mhorimoto/M304B/InputSwitch.kicad_sch

## KiCad design InputSwitch.kicad_sch (2024-06-09)

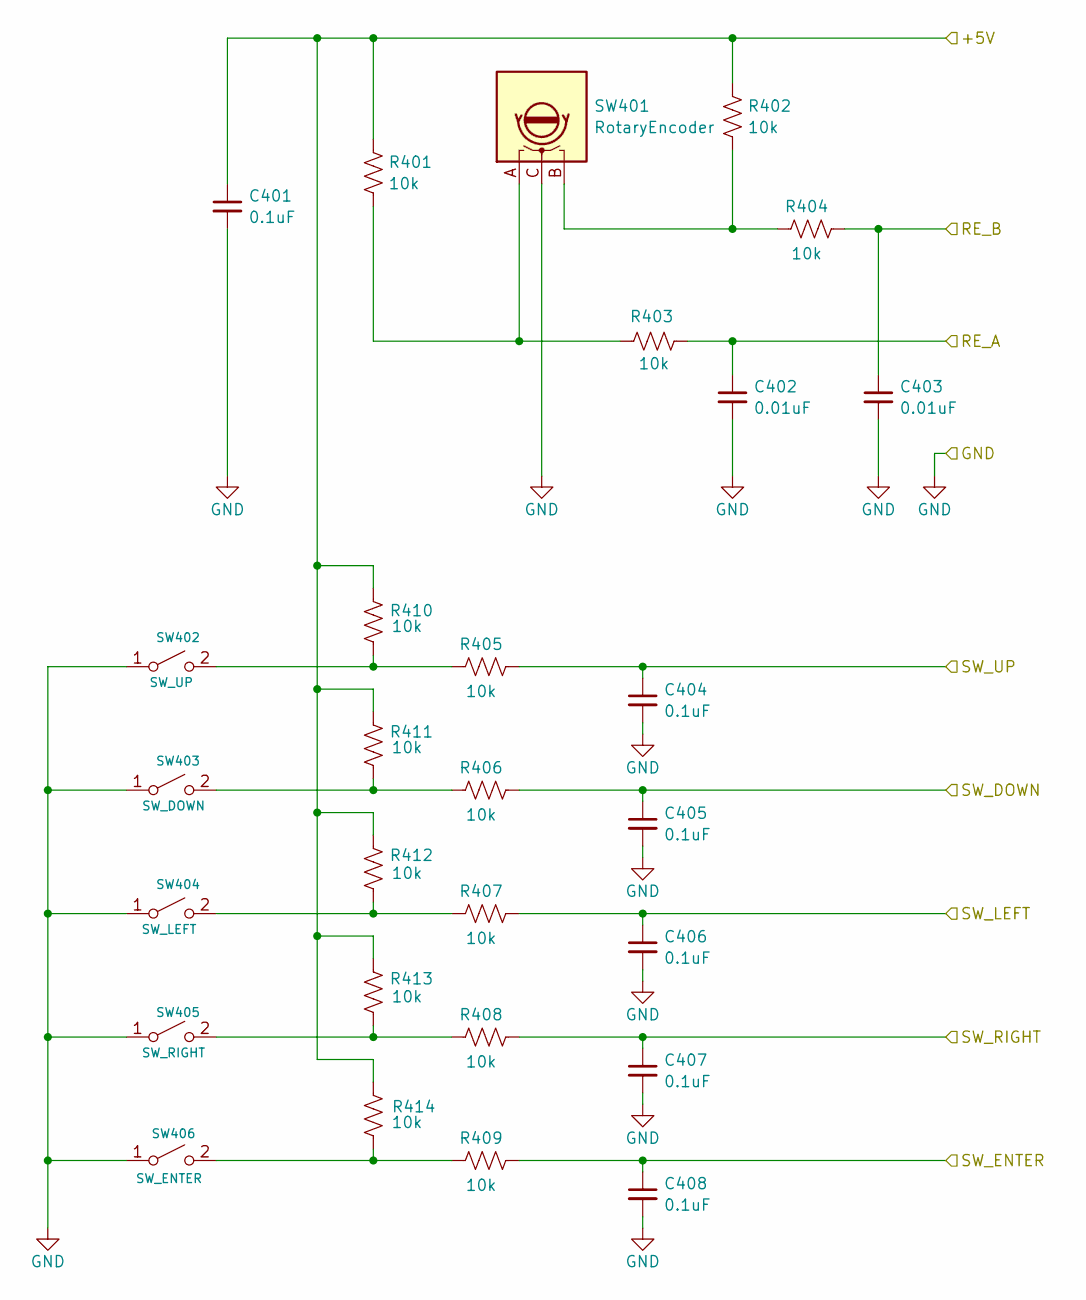
[picture p6: schematic InputSwitch.kicad_sch]

Parts:
C401, C404, C405, C406, C407, C408: 0.1uF; C_Disc_D3.0mm_W2.0mm_P2.50mm
C402, C403: 0.01uF; C_Disc_D3.0mm_W2.0mm_P2.50mm
R401, R402, R403, R404, R405, R406, R407, R408, R409, R410, R411, R412, R413, R414: 10k
SW401: RotaryEncoder; RotaryEncoder_Alps_EC12E_Vertical_H20mm
SW402: SW_UP; TVDT18-050
SW403: SW_DOWN; TVDT18-050
SW404: SW_LEFT; TVDT18-050
SW405: SW_RIGHT; TVDT18-050
SW406: SW_ENTER; TVDT18-050

Connections:
+5V: C401.1, R401.1, R402.1, R410.2, R411.2, R412.2, R413.2, R414.2
GND: C401.2, C402.2, C403.2, C404.2, C405.2, C406.2, C407.2, C408.2, SW401.C, SW402.1 (A), SW403.1 (A), SW404.1 (A), SW405.1 (A), SW406.1 (A)
unnamed: R401.2, R403.1, SW401.A
unnamed: R402.2, R404.1, SW401.B
unnamed: R405.1, R410.1, SW402.2 (B)
unnamed: R406.1, R411.1, SW403.2 (B)
unnamed: R407.1, R412.1, SW404.2 (B)
unnamed: R408.1, R413.1, SW405.2 (B)
unnamed: R409.1, R414.1, SW406.2 (B)
RE_A: C402.1, R403.2
RE_B: C403.1, R404.2
SW_DOWN: C405.1, R406.2
SW_ENTER: C408.1, R409.2
SW_LEFT: C406.1, R407.2
SW_RIGHT: C407.1, R408.2
SW_UP: C404.1, R405.2
