mhorimoto/M304B/M304B.kicad_sch

## KiCad design M304B.kicad_sch (2024-06-09)

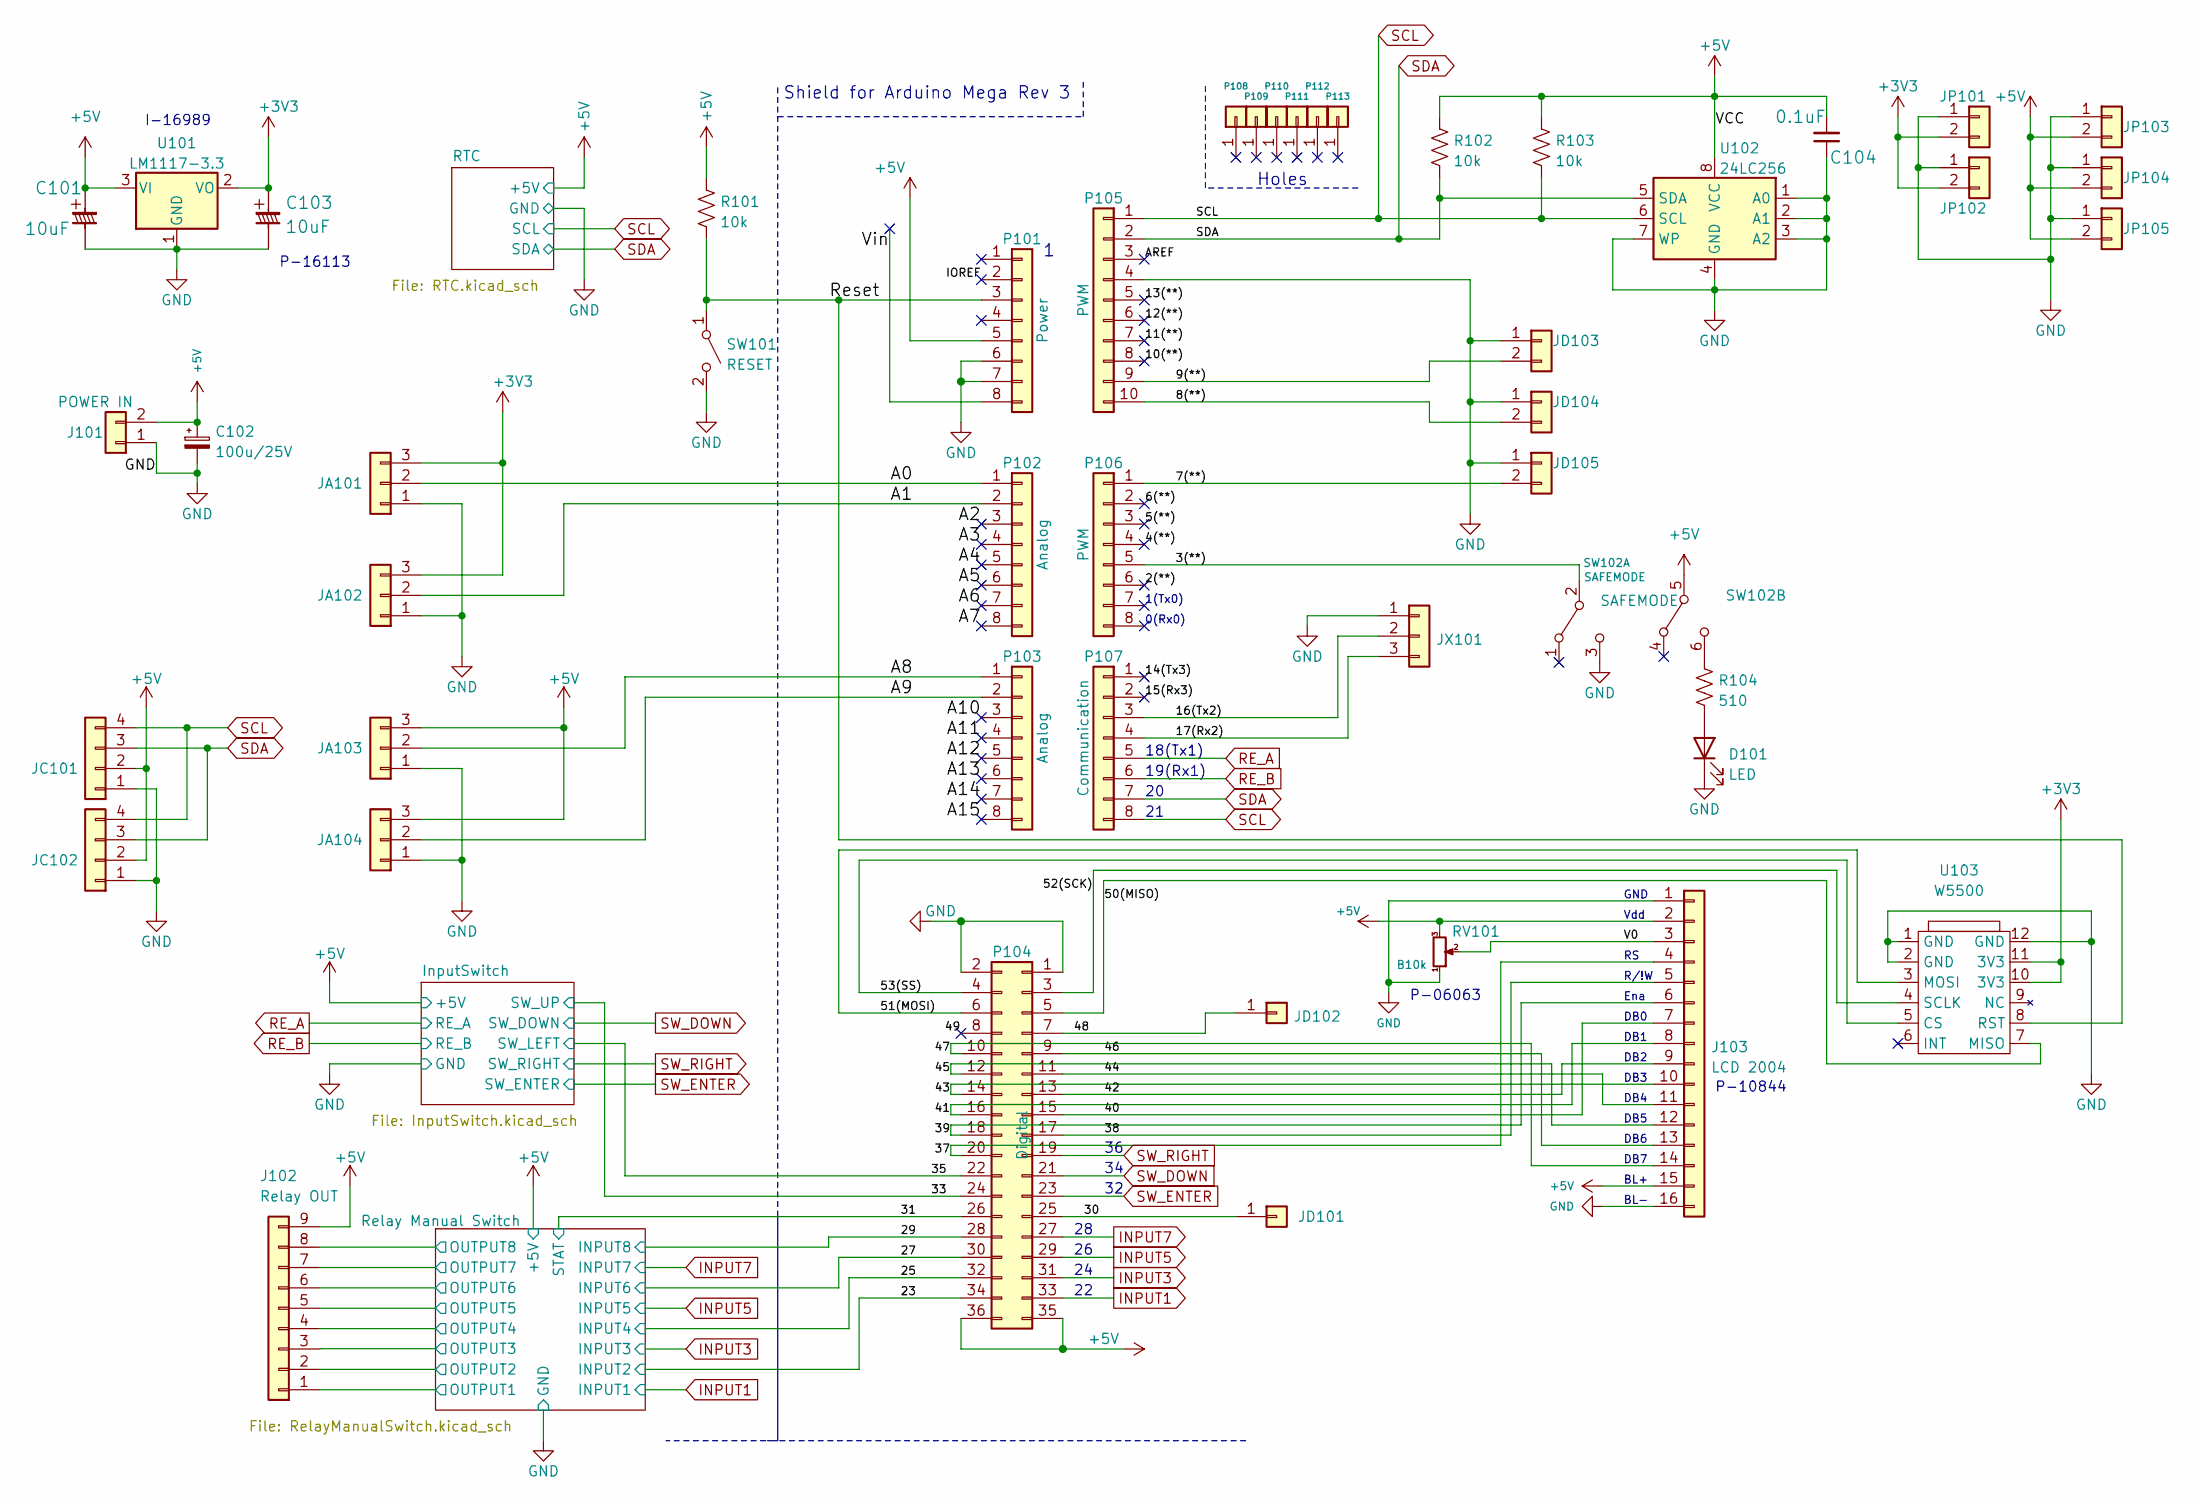
[picture p7: schematic M304B.kicad_sch]

Parts:
C101, C103: 10uF; C_1210_3225Metric_Pad1.33x2.70mm_HandSolder
C102: 100u/25V; CP_Radial_D5.0mm_P2.00mm
C104: 0.1uF; C_Disc_D3.0mm_W2.0mm_P2.50mm
D101: LED; LED_D3.0mm
J101: POWER IN; JST_VH_B2P-VH_1x02_P3.96mm_Vertical
J102: Relay OUT; JST_XH_B9B-XH-A_1x09_P2.50mm_Vertical
J103: LCD 2004; PinSocket_1x16_P2.54mm_Vertical
JA101, JA102, JA103, JA104: Conn_01x03; JST_XH_B3B-XH-A_1x03_P2.50mm_Vertical
JC101, JC102: Conn_01x04; JST_XH_B4B-XH-A_1x04_P2.50mm_Vertical
JD101, JD102: Conn_01x01; Pin_D0.9mm_L10.0mm_W2.4mm_FlatFork
JD103, JD104, JD105: Conn_01x02; JST_XH_B2B-XH-A_1x02_P2.50mm_Vertical
JP101, JP102, JP103, JP104, JP105: Conn_01x02; JST_XH_B2B-XH-A_1x02_P2.50mm_Vertical
JX101: Conn_01x03; JST_XH_B3B-XH-A_1x03_P2.50mm_Vertical
P101: Power; PinHeader_1x08_P2.54mm_Vertical
P102, P103: Analog; PinHeader_1x08_P2.54mm_Vertical
P104: Digital; PinHeader_2x18_P2.54mm_Vertical
P105: PWM; PinHeader_1x10_P2.54mm_Vertical
P106: PWM; PinHeader_1x08_P2.54mm_Vertical
P107: Communication; PinHeader_1x08_P2.54mm_Vertical
P108, P109, P110, P111, P112, P113: CONN_01X01; Arduino_1pin
R101, R102, R103: 10k; R_Axial_DIN0207_L6.3mm_D2.5mm_P7.62mm_Horizontal
R104: 510; R_Axial_DIN0207_L6.3mm_D2.5mm_P7.62mm_Horizontal
RV101: B10k; Potentiometer_Runtron_RM-065_Vertical
SW101: RESET; TVDT18-050
SW102: SAFEMODE; 2MD1T2B4M2QNS
U101: LM1117-3.3; SOT-223-3_TabPin2
U102: 24LC256; DIP-8_W7.62mm_LongPads
U103: W5500

Connections:
2(**): P106.6
3(**): P106.5, SW102.2 (B)
4(**): P106.4
5(**): P106.3
6(**): P106.2
7(**): JD105.2, P106.1
8(**): JD104.2, P105.10
9(**): JD103.2, P105.9
10(**): P105.8
11(**): P105.7
12(**): P105.6
13(**): P105.5
14(Tx3): P107.1
15(Rx3): P107.2
16(Tx2): JX101.2, P107.3
17(Rx2): JX101.3, P107.4
23: P104.34
25: P104.32
27: P104.30
29: P104.28
30: JD101.1, P104.25
31: P104.26
33: P104.24
35: P104.22
37: J103.4, P104.20
38: J103.5, P104.17
39: J103.6, P104.18
40: J103.7, P104.15
41: J103.8, P104.16
42: J103.9, P104.13
43: J103.10, P104.14
44: J103.11, P104.11
45: J103.12, P104.12
46: J103.13, P104.9
47: J103.14, P104.10
48: JD102.1, P104.7
49: P104.8
50(MISO): P104.5, U103.7 (MISO)
51(MOSI): P104.6, U103.3 (MOSI)
52(SCK): P104.3, U103.4 (SCLK)
53(SS): P104.4, U103.5 (CS)
+3V3: C103.2, JA101.3, JA102.3, JP101.2, JP102.2, U101.2 (VO), U103.10 (3V3), U103.11 (3V3)
+5V: C101.2, C102.1, C104.2, J101.2, J102.9, J103.2, J103.15, JA103.3, JA104.3, JC101.2, JC102.2, JP103.2, JP104.2, JP105.2, P101.5, P104.35, P104.36, R101.2, R102.1, R103.1, RV101.3, SW102.5 (B), U101.3 (VI), U102.8 (VCC)
A0: JA101.2, P102.1
A1: JA102.2, P102.2
A2: P102.3
A3: P102.4
A4: P102.5
A5: P102.6
A6: P102.7
A7: P102.8
A8: JA103.2, P103.1
A9: JA104.2, P103.2
A10: P103.3
A11: P103.4
A12: P103.5
A13: P103.6
A14: P103.7
A15: P103.8
AREF: P105.3
GND: C101.1, C102.2, C103.1, C104.1, D101.1 (K), J101.1, J103.1, J103.16, JA101.1, JA102.1, JA103.1, JA104.1, JC101.1, JC102.1, JD103.1, JD104.1, JD105.1, JP101.1, JP102.1, JP103.1, JP104.1, JP105.1, JX101.1, P101.6, P101.7, P104.1, P104.2, P105.4, RV101.1, SW101.2 (B), SW102.3 (C), U101.1 (GND), U102.1 (A0), U102.2 (A1), U102.3 (A2), U102.4 (GND), U102.7 (WP), U103.1 (GND), U103.2 (GND), U103.12 (GND)
INPUT1: P104.33
INPUT3: P104.31
INPUT5: P104.29
INPUT7: P104.27
IOREF: P101.2
unnamed: D101.2 (A), R104.2
unnamed: R104.1, SW102.6 (C)
OUTPUT1: J102.1
OUTPUT2: J102.2
OUTPUT3: J102.3
OUTPUT4: J102.4
OUTPUT5: J102.5
OUTPUT6: J102.6
OUTPUT7: J102.7
OUTPUT8: J102.8
RE_A: P107.5
RE_B: P107.6
Reset: P101.3, R101.1, SW101.1 (A), U103.8 (RST)
SCL: JC101.4, JC102.4, P105.1, P107.8, R103.2, U102.6 (SCL)
SDA: JC101.3, JC102.3, P105.2, P107.7, R102.2, U102.5 (SDA)
SW_DOWN: P104.21
SW_ENTER: P104.23
SW_RIGHT: P104.19
V0: J103.3, RV101.2
Vin: P101.8

Notes on the sheet:
DB5
P-16113
P-10844
18(Tx1)
DB4
Ena
DB6
0(Rx0)
I-16989
DB3
Vdd
DB0
R/!W
P-06063
DB1
19(Rx1)
GND
1(Tx0)
Holes
BL+
DB2
DB7
BL-
Shield for Arduino Mega Rev 3
