mhorimoto/M304B/RTC.kicad_sch

## KiCad design RTC.kicad_sch (2024-06-09)

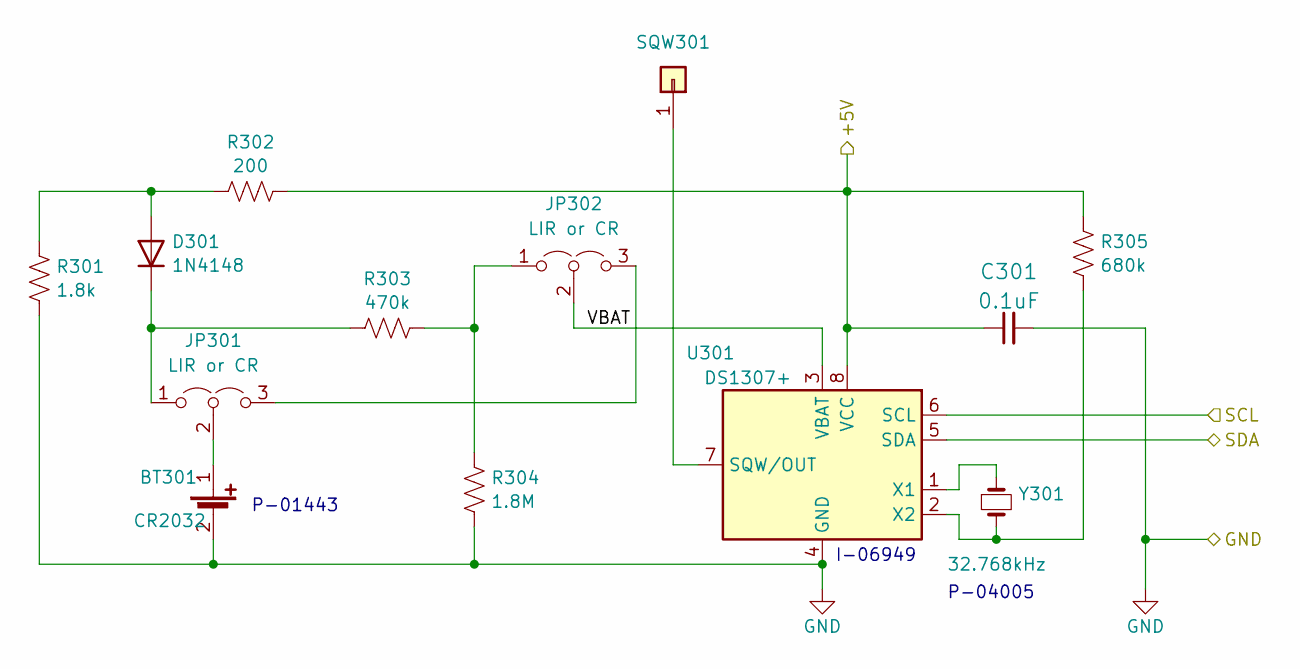
[picture p8: schematic RTC.kicad_sch]

Parts:
BT301: CR2032; CH74-2032LF
C301: 0.1uF; C_Disc_D3.0mm_W2.0mm_P2.50mm
D301: 1N4148; D_DO-35_SOD27_P7.62mm_Horizontal
JP301, JP302: LIR or CR; PinHeader_1x03_P2.54mm_Vertical
R301: 1.8k; R_Axial_DIN0207_L6.3mm_D2.5mm_P7.62mm_Horizontal
R302: 200; R_Axial_DIN0207_L6.3mm_D2.5mm_P7.62mm_Horizontal
R303: 470k; R_Axial_DIN0207_L6.3mm_D2.5mm_P7.62mm_Horizontal
R304: 1.8M; R_Axial_DIN0207_L6.3mm_D2.5mm_P7.62mm_Horizontal
R305: 680k; R_Axial_DIN0207_L6.3mm_D2.5mm_P7.62mm_Horizontal
SQW301: Conn_01x01; Pin_D0.9mm_L10.0mm_W2.4mm_FlatFork
U301: DS1307+; DIP-8_W7.62mm_LongPads
Y301: 32.768kHz; Crystal_C26-LF_D2.1mm_L6.5mm_Horizontal

Connections:
+5V: C301.1, R302.2, R305.1, U301.8 (VCC)
GND: BT301.2 (-), C301.2, R301.2, R304.2, U301.4 (GND)
unnamed: BT301.1 (+), JP301.2 (C)
unnamed: D301.1 (K), JP301.1 (A), R303.1
unnamed: D301.2 (A), R301.1, R302.1
unnamed: JP301.3 (B), JP302.3 (B)
unnamed: JP302.1 (A), R303.2, R304.1
unnamed: R305.2, U301.2 (X2), Y301.2
unnamed: SQW301.1, U301.7 (SQW/OUT)
unnamed: U301.1 (X1), Y301.1
SCL: U301.6 (SCL)
SDA: U301.5 (SDA)
VBAT: JP302.2 (C), U301.3 (VBAT)

Notes on the sheet:
P-01443
I-06949
P-04005
