mhorimoto/M304B/RelayManualSwitch.kicad_sch

## KiCad design RelayManualSwitch.kicad_sch (2024-06-09)

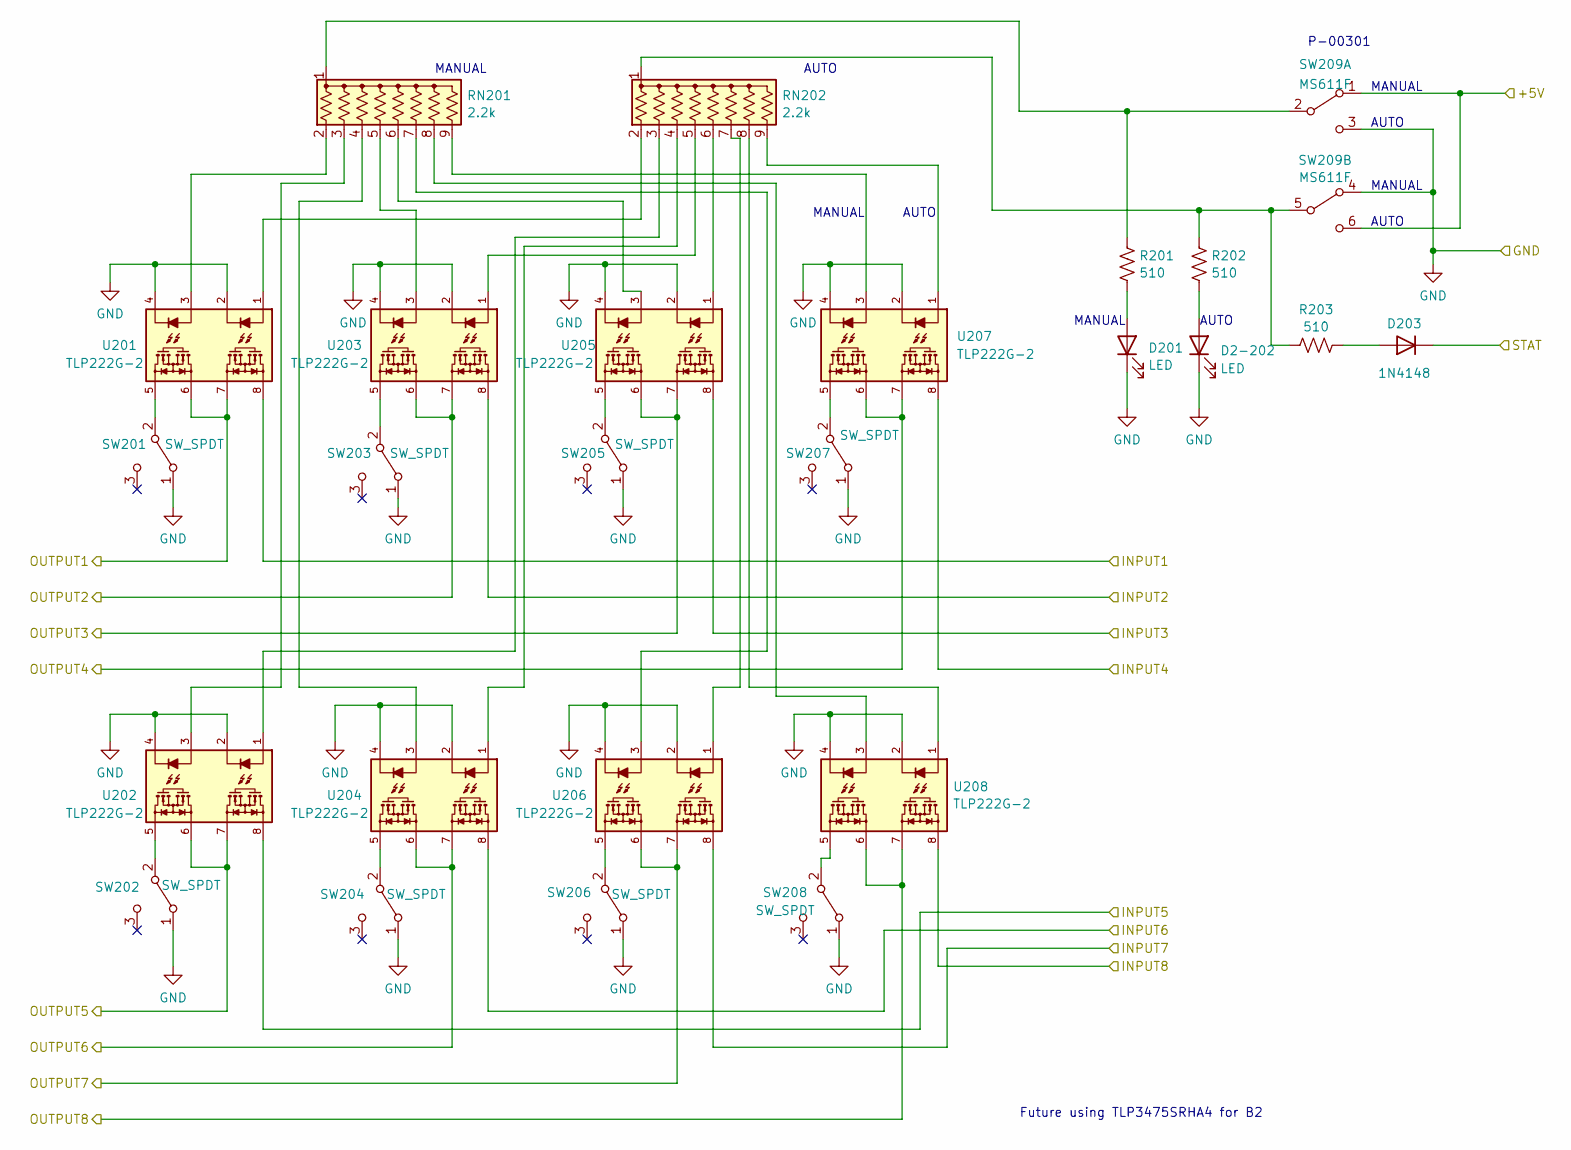
[picture p9: schematic RelayManualSwitch.kicad_sch]

Parts:
D2-202, D201: LED; LED_D3.0mm
D203: 1N4148; D_DO-35_SOD27_P7.62mm_Horizontal
R201, R202, R203: 510; R_Axial_DIN0207_L6.3mm_D2.5mm_P7.62mm_Horizontal
RN201, RN202: 2.2k; R_Array_SIP9
SW201, SW202, SW203, SW204, SW205, SW206, SW207, SW208: SW_SPDT; 2MS1T1B4M2QES
SW209: MS611F; 2MD1T2B4M2QNS
U201, U202, U203, U204, U205, U206, U207, U208: TLP222G-2; TLP222A-2

Connections:
+5V: SW209.1 (A), SW209.6 (C)
GND: D2-202.1 (K), D201.1 (K), SW201.1 (A), SW202.1 (A), SW203.1 (A), SW204.1 (A), SW205.1 (A), SW206.1 (A), SW207.1 (A), SW208.1 (A), SW209.3 (C), SW209.4 (A), U201.2, U201.4, U202.2, U202.4, U203.2, U203.4, U204.2, U204.4, U205.2, U205.4, U206.2, U206.4, U207.2, U207.4, U208.2, U208.4
INPUT1: U201.8
INPUT2: U203.8
INPUT3: U205.8
INPUT4: U207.8
INPUT5: U202.8
INPUT6: U204.8
INPUT7: U206.8
INPUT8: U208.8
unnamed: D2-202.2 (A), R202.2
unnamed: D201.2 (A), R201.2
unnamed: D203.2 (A), R203.2
unnamed: R201.1, RN201.1 (common), SW209.2 (B)
unnamed: R202.1, R203.1, RN202.1 (common), SW209.5 (B)
unnamed: RN201.2 (R1), U201.3
unnamed: RN201.3 (R2), U202.3
unnamed: RN201.4 (R3), U204.3
unnamed: RN201.5 (R4), U203.3
unnamed: RN201.6 (R5), U205.3
unnamed: RN201.7 (R6), U206.3
unnamed: RN201.8 (R7), U208.3
unnamed: RN201.9 (R8), U207.3
unnamed: RN202.2 (R1), U201.1
unnamed: RN202.3 (R2), U202.1
unnamed: RN202.4 (R3), U204.1
unnamed: RN202.5 (R4), U203.1
unnamed: RN202.6 (R5), U205.1
unnamed: RN202.7 (R6), U206.1
unnamed: RN202.8 (R7), U208.1
unnamed: RN202.9 (R8), U207.1
unnamed: SW201.2 (B), U201.5
unnamed: SW202.2 (B), U202.5
unnamed: SW203.2 (B), U203.5
unnamed: SW204.2 (B), U204.5
unnamed: SW205.2 (B), U205.5
unnamed: SW206.2 (B), U206.5
unnamed: SW207.2 (B), U207.5
unnamed: SW208.2 (B), U208.5
OUTPUT1: U201.6, U201.7
OUTPUT2: U203.6, U203.7
OUTPUT3: U205.6, U205.7
OUTPUT4: U207.6, U207.7
OUTPUT5: U202.6, U202.7
OUTPUT6: U204.6, U204.7
OUTPUT7: U206.6, U206.7
OUTPUT8: U208.6, U208.7
STAT: D203.1 (K)

Notes on the sheet:
AUTO
MANUAL
Future using TLP3475SRHA4 for B2
P-00301
